cjtrowbridge/All-Seeing-Eye/3d models/design/cc1101/c2f52c2afb3fe4cf12543e919a84cf52887175e8_2_690x293.png

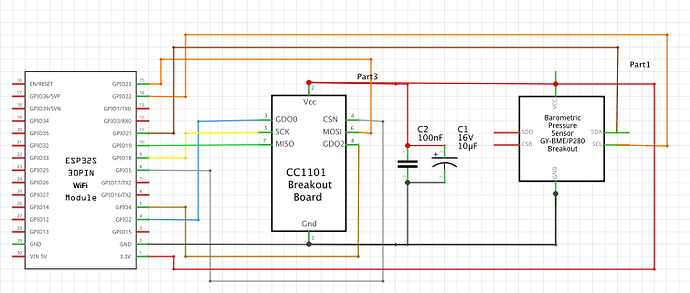
3d models/design/cc1101/c2f52c2afb3fe4cf12543e919a84cf52887175e8_2_690x293.png
