cjtrowbridge/All-Seeing-Eye/3d models/design/cc1101/images.jpg

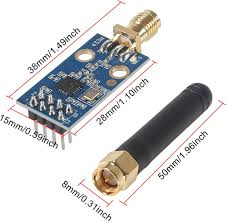
3d models/design/cc1101/images.jpg
