cjtrowbridge/All-Seeing-Eye/3d models/design/esp/616AZvK9qwL._AC_SL1200_.jpg

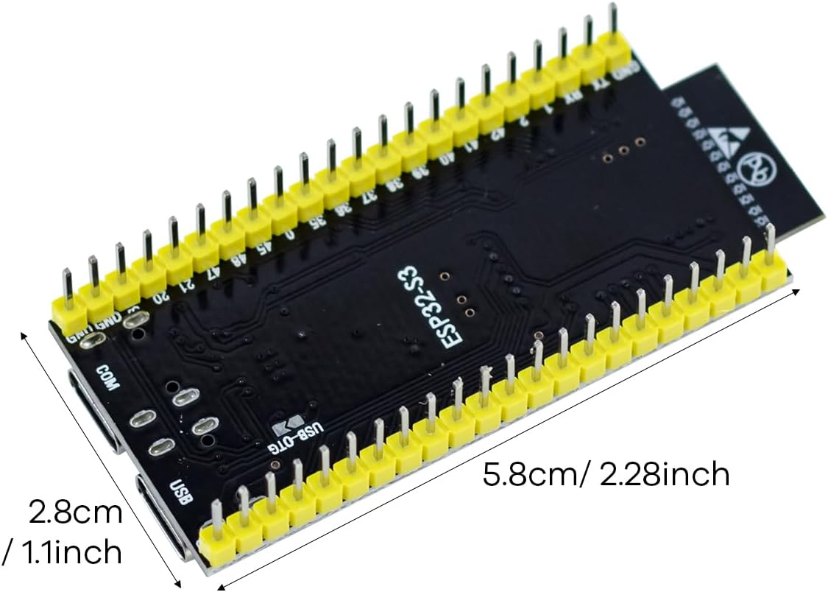
3d models/design/esp/616AZvK9qwL._AC_SL1200_.jpg
