cjtrowbridge/All-Seeing-Eye/3d models/design/esp/PXL_20260108_181501124.jpg

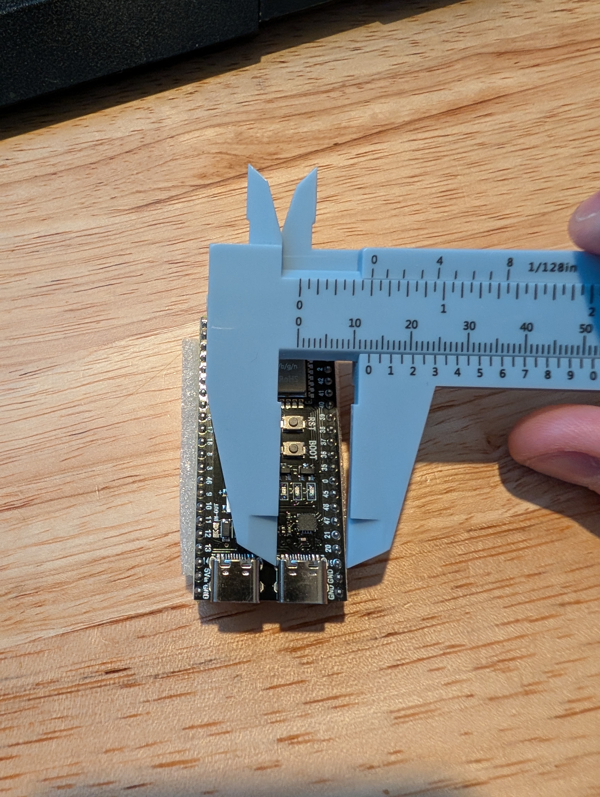
3d models/design/esp/PXL_20260108_181501124.jpg
