cjtrowbridge/All-Seeing-Eye/3d models/design/esp/PXL_20260108_181535649.jpg

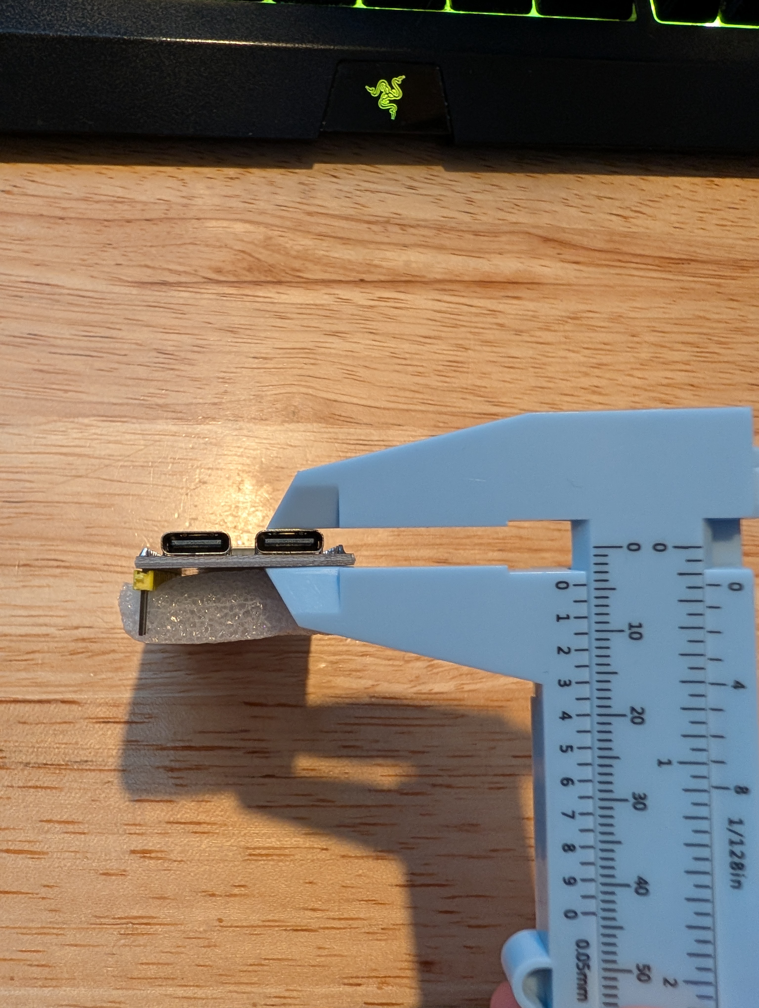
3d models/design/esp/PXL_20260108_181535649.jpg
