cjtrowbridge/All-Seeing-Eye/3d models/design/esp/PXL_20260110_050137347.jpg

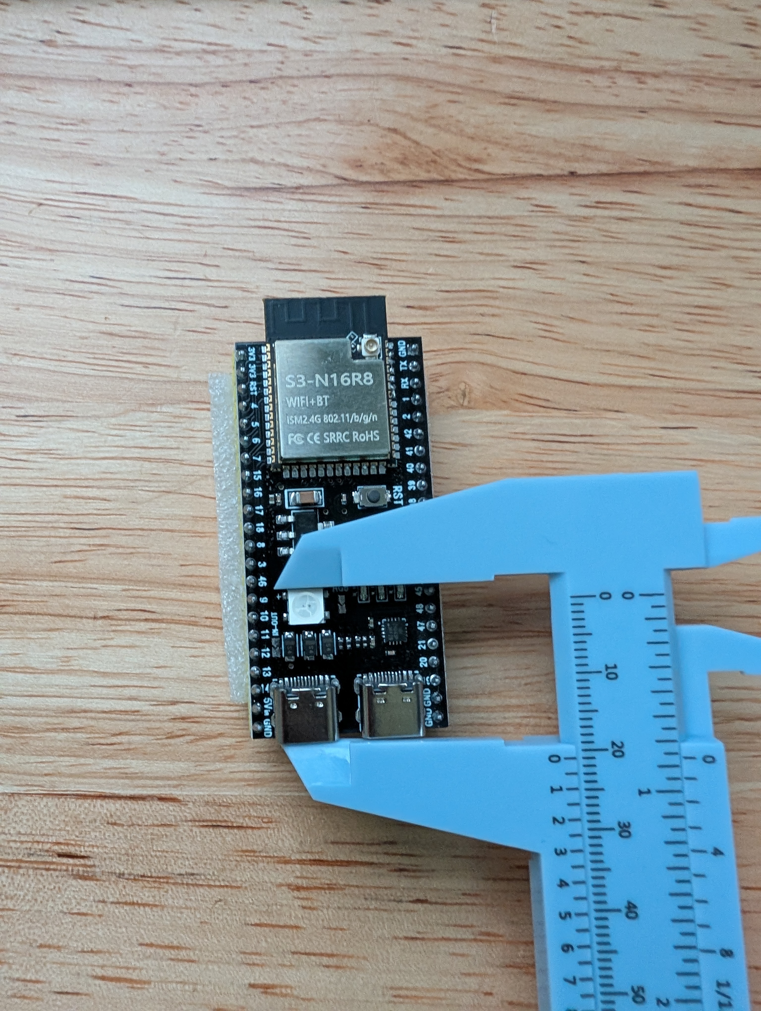
3d models/design/esp/PXL_20260110_050137347.jpg
