cjtrowbridge/All-Seeing-Eye/3d models/design/esp/PXL_20260110_050159167.jpg

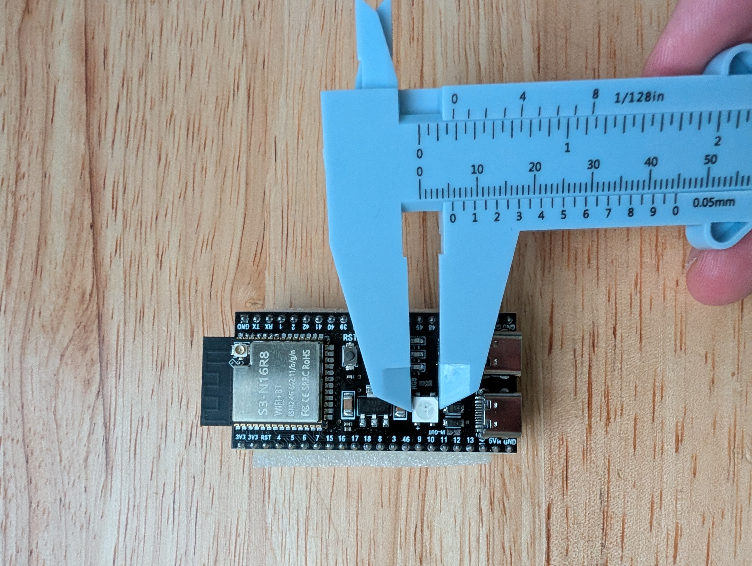
3d models/design/esp/PXL_20260110_050159167.jpg
