cjtrowbridge/All-Seeing-Eye/firmware/AllSeeingEye/src/WebStatic.h

#ifndef WEBSTATIC_H
#define WEBSTATIC_H

#include <Arduino.h>

const uint32_t index_html_gz_len = 15602;
const uint8_t index_html_gz[] PROGMEM = {
0x1F, 0x8B, 0x08, 0x00, 0xB3, 0xF0, 0x6A, 0x69, 0x02, 0xFF, 0xED, 0x7D, 0xED, 0x72, 0xE3, 0x46, 
0x92, 0xE0, 0xFF, 0x8D, 0xD8, 0x77, 0x28, 0xD3, 0x1E, 0x13, 0x6C, 0x93, 0x14, 0xA5, 0x6E, 0xF5, 
0xB6, 0xC9, 0x96, 0xBC, 0xB2, 0xA4, 0xB6, 0x75, 0xD3, 0x2D, 0xE9, 0x5A, 0xEA, 0xF1, 0x4E, 0x78, 
0x1D, 0xDB, 0x20, 0x59, 0xA4, 0xE0, 0x06, 0x01, 0x1A, 0x00, 0x25, 0xD1, 0xBD, 0xFC, 0x71, 0x4F, 
0x30, 0x71, 0x7F, 0x2F, 0x36, 0xE2, 0xE2, 0xFE, 0xDD, 0x23, 0xEC, 0xF3, 0xCC, 0x0B, 0xEC, 0x3D, 
0xC2, 0x65, 0x66, 0x15, 0x80, 0x02, 0x50, 0x55, 0x00, 0xD5, 0x1A, 0xCF, 0x4E, 0xC4, 0xB6, 0x6C, 
0x89, 0x04, 0xAA, 0xB2, 0xAA, 0xB2, 0xB2, 0xB2, 0xF2, 0xAB, 0xB2, 0x5E, 0x7E, 0x76, 0x72, 0x71, 
0x7C, 0xFD, 0xC7, 0xCB, 0x53, 0x76, 0x93, 0x2C, 0xFC, 0xC3, 0xBF, 0xFF, 0xBB, 0x97, 0xF8, 0x97, 
0xF9, 0x6E, 0x30, 0x3F, 0x68, 0xF1, 0xA0, 0x45, 0x4F, 0xB8, 0x3B, 0x85, 0xBF, 0x0C, 0xFE, 0xBD, 
0x5C, 0xF0, 0xC4, 0x65, 0x93, 0x1B, 0x37, 0x8A, 0x79, 0x72, 0xD0, 0x7A, 0x77, 0xFD, 0xAA, 0xF7, 
0xA2, 0x55, 0x78, 0x17, 0xB8, 0x0B, 0x7E, 0xD0, 0xBA, 0xF5, 0xF8, 0xDD, 0x32, 0x8C, 0x92, 0x16, 
0x9B, 0x84, 0x41, 0xC2, 0x03, 0x28, 0x7B, 0xE7, 0x4D, 0x93, 0x9B, 0x83, 0x29, 0xBF, 0xF5, 0x26, 
0xBC, 0x47, 0x5F, 0xBA, 0xCC, 0x0B, 0xBC, 0xC4, 0x73, 0xFD, 0x5E, 0x3C, 0x71, 0x7D, 0x7E, 0xB0, 
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
0xB9, 0xE3, 0x85, 0x11, 0xE1, 0x3F, 0xD7, 0xF7, 0xE6, 0x41, 0xCF, 0x03, 0x44, 0x03, 0x7E, 0x71, 
0x75, 0xF0, 0xA8, 0x54, 0x22, 0xA3, 0xC4, 0x24, 0x09, 0x17, 0x80, 0xB5, 0xE5, 0x3D, 0x8B, 0x43, 
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
};

#endif
