cjtrowbridge/All-Seeing-Eye/firmware/AllSeeingEye/src/WebServer.cpp

#include "WebServer.h"
#include <LittleFS.h>
#include "WebStatic.h" // Include generated HTML header
#include "BuildVersion.h" // Include generated Build ID
#include "Kernel.h" // For status access
#include "HAL.h" // Add HAL for Hardware Status
#include "Logger.h" // Add Logger
#include "RingBuffer.h" // Add RingBuffer
#include "PluginManager.h" // Add PluginManager
#include "PeerManager.h" // Add PeerManager
#include "Config.h" // Add Config
#include "AsyncJson.h" 
#include <ArduinoJson.h>
#include "Scheduler.h" // Add scheduler
#include "Geolocation.h"
#include "BleRangingManager.h"
#include <HTTPClient.h>

WebServerManager& WebServerManager::instance() {
    static WebServerManager _instance;
    return _instance;
}

WebServerManager::WebServerManager() : _server(80) {}

void WebServerManager::begin() {
    DefaultHeaders::Instance().addHeader("Access-Control-Allow-Origin", "*");
    
    setupRoutes();
    _server.begin();
    Serial.println("[Web] Async Server Started on Port 80");
}

void WebServerManager::setupRoutes() {
    // --------------------------------------------------
    // 1. Specific API Endpoints (Register First)
    // --------------------------------------------------

    // API: Status
    _server.on("/api/status", HTTP_GET, [this](AsyncWebServerRequest *request){
        static unsigned long lastStatusLog = 0;
        if (millis() - lastStatusLog > 10000) {
            Logger::instance().info("API", "GET /api/status");
            lastStatusLog = millis();
        }
        request->send(200, "application/json", this->getCachedStatus());
    });

    // API: Configuration (GET)
    _server.on("/api/config", HTTP_GET, [](AsyncWebServerRequest *request){
        Logger::instance().info("API", "GET /api/config");
        String response = Config::instance().getAllAsJson();
        request->send(200, "application/json", response);
    });

    // API: Configuration (POST)
    AsyncCallbackJsonWebHandler *handler = new AsyncCallbackJsonWebHandler("/api/config", [](AsyncWebServerRequest *request, JsonVariant &json) {
        Logger::instance().info("API", "POST /api/config");
        String jsonStr;
        serializeJson(json, jsonStr);
        
        if (Config::instance().updateFromJson(jsonStr)) {
            Logger::instance().info("Config", "Settings updated via API");
            JsonObject obj = json.as<JsonObject>();
            if (obj.containsKey("timezone")) {
                String timezone = Config::instance().getTimezone();
                Kernel::instance().applyTimezone(timezone);
                Logger::instance().info("Kernel", "Timezone updated: %s", timezone.c_str());
            }
            request->send(200, "application/json", "{\"status\":\"success\", \"message\":\"Config Updated. Reboot to apply network changes.\"}");
            // Optional: Config::instance().save(); // Preferences are auto-saved in close/put
        } else {
            Logger::instance().error("Config", "JSON parsing failed");
            request->send(400, "application/json", "{\"status\":\"error\", \"message\":\"Invalid JSON\"}");
        }
    });
    _server.addHandler(handler);

    // API: File System Index
    _server.on("/api/fs", HTTP_GET, [](AsyncWebServerRequest *request){
        Logger::instance().info("API", "GET /api/fs");
        JsonDocument doc;
        JsonArray files = doc.to<JsonArray>();

        File root = LittleFS.open("/");
        File file = root.openNextFile();
        while(file){
            JsonObject f = files.add<JsonObject>();
            f["name"] = String(file.name());
            f["size"] = file.size();
            file = root.openNextFile();
        }
        
        String response;
        serializeJson(doc, response);
        request->send(200, "application/json", response);
    });

    // API: Peers (Discovery)
    _server.on("/api/peers", HTTP_GET, [](AsyncWebServerRequest *request){
        Logger::instance().info("API", "GET /api/peers");
        // Passive Discovery: Check who is calling us
        PeerManager::instance().trackIncomingRequest(request->client()->remoteIP().toString());
        
        String response = PeerManager::instance().getPeersAsJson();
        request->send(200, "application/json", response);
    });

    // API: BLE Ranging (Latest Scan)
    _server.on("/api/ranging/ble", HTTP_GET, [](AsyncWebServerRequest *request){
        Logger::instance().info("API", "GET /api/ranging/ble");
        JsonDocument doc;
        JsonObject ble = doc.to<JsonObject>();
        BleRangingManager::instance().populateStatus(ble);
        String response;
        serializeJson(doc, response);
        request->send(200, "application/json", response);
    });

    // API: Utils - Ping
    _server.on("/api/ping", HTTP_GET, [](AsyncWebServerRequest *request){
        if (request->hasParam("target")) {
            String target = request->getParam("target")->value();
            Logger::instance().info("API", "GET /api/ping target=%s", target.c_str());
            bool result = PeerManager::instance().pingHost(target);
            
            JsonDocument doc;
            doc["target"] = target;
            doc["reachable"] = result;
            
            String res;
            serializeJson(doc, res);
            request->send(200, "application/json", res);
        } else {
            Logger::instance().warn("API", "GET /api/ping missing target");
            request->send(400, "application/json", "{\"error\":\"Missing 'target' parameter\"}");
        }
    });

    // API: System Head Logs (Startup Logs)
    // NOTE: Must be registered BEFORE /api/logs to avoid routing shadow
    _server.on("/api/logs/head", HTTP_GET, [](AsyncWebServerRequest *request){
        static unsigned long lastHeadLogsLog = 0;
        if (millis() - lastHeadLogsLog > 5000) {
            Logger::instance().info("API", "GET /api/logs/head");
            lastHeadLogsLog = millis();
        }
        JsonDocument doc;
        JsonArray logs = doc.to<JsonArray>();
        
        std::deque<String> logBuffer = Logger::instance().getHeadLogs();
        
        for(const auto& line : logBuffer) {
            logs.add(line);
        }
        
        String response;
        serializeJson(doc, response);
        request->send(200, "application/json", response);
    });

    // API: System Logs
    _server.on("/api/logs", HTTP_GET, [](AsyncWebServerRequest *request){
        static unsigned long lastLogsLog = 0;
        if (millis() - lastLogsLog > 5000) {
            Logger::instance().info("API", "GET /api/logs");
            lastLogsLog = millis();
        }
        JsonDocument doc;
        JsonArray logs = doc.to<JsonArray>();
        
        std::deque<String> logBuffer = Logger::instance().getLogs();
        
        // Return logs in insertion order
        for(const auto& line : logBuffer) {
            logs.add(line);
        }
        
        String response;
        serializeJson(doc, response);
        request->send(200, "application/json", response);
    });

    // --------------------------------------------------
    // API: Task Registry (Phase 5.1)
    // --------------------------------------------------

    // GET /api/task - Discovery
    _server.on("/api/task", HTTP_GET, [](AsyncWebServerRequest *request){
        Logger::instance().info("API", "GET /api/task");
        JsonDocument doc;
        JsonArray arr = doc.to<JsonArray>();
        
        std::vector<TaskDefinition> tasks = PluginManager::instance().getTaskCatalog();
        
        for(const auto& t : tasks) {
            JsonObject obj = arr.add<JsonObject>();
            obj["id"] = t.id;
            obj["name"] = t.name;
            obj["description"] = t.description;
            obj["plugin"] = t.pluginName;
            obj["link"] = t.endpoint;
            if (!t.inputs.empty()) {
                JsonArray inputs = obj.createNestedArray("inputs");
                for (const auto& input : t.inputs) {
                    JsonObject inputObj = inputs.add<JsonObject>();
                    inputObj["name"] = input.name;
                    inputObj["label"] = input.label;
                    inputObj["type"] = input.type;
                    if (input.required) {
                        inputObj["required"] = true;
                    }
                    if (input.defaultType == INPUT_VALUE_NUMBER) {
                        inputObj["default"] = input.defaultNumber;
                    } else if (input.defaultType == INPUT_VALUE_BOOL) {
                        inputObj["default"] = input.defaultBool;
                    } else if (input.defaultType == INPUT_VALUE_TEXT) {
                        inputObj["default"] = input.defaultText;
                    }
                    if (input.hasStep) {
                        inputObj["step"] = input.step;
                    }
                    if (input.hasMin) {
                        inputObj["min"] = input.min;
                    }
                    if (input.hasMax) {
                        inputObj["max"] = input.max;
                    }
                    if (!input.options.empty()) {
                        JsonArray options = inputObj.createNestedArray("options");
                        for (const auto& opt : input.options) {
                            JsonObject optObj = options.add<JsonObject>();
                            optObj["label"] = opt.label;
                            optObj["value"] = opt.value;
                        }
                    }
                }
            }
        }

        String response;
        serializeJson(doc, response);
        request->send(200, "application/json", response);
    });

    // POST /api/task/{taskId} - Execution
    // Note: We use a wildcard handler because AsyncWebServer doesn't do path params easily for *all* subpaths
    // But we defined specific endpoints in the catalog, so we can just match startsWith or use specific handlers.
    // For simplicity, we will register a generic handler for POST requests and parse the URL.
    
    // Instead of one generic handler which is messy, let's implement the specific routes from the catalog?
    // Cons: Duplication.
    // Pros: Explicit.
    
    // Better: One Handler for /api/task/* to give instructions
    _server.on("/api/task", HTTP_POST, [](AsyncWebServerRequest *request){
         request->send(400, "application/json", "{\"error\":\"Use specific task endpoints e.g. /api/task/ble-ranging/survey\"}");
    });
    
    // Loop to register handlers for catalog items
    std::vector<TaskDefinition> tasks = PluginManager::instance().getTaskCatalog();
    for(const auto& t : tasks) {
         AsyncCallbackJsonWebHandler *h = new AsyncCallbackJsonWebHandler(t.endpoint.c_str(), [t](AsyncWebServerRequest *request, JsonVariant &json) {
            Logger::instance().info("API", "Starting Task: %s", t.id.c_str());
            JsonObject params = json.as<JsonObject>();
            if (PluginManager::instance().startTask(t.id, params)) {
                 request->send(200, "application/json", "{\"status\":\"started\", \"taskId\":\"" + t.id + "\"}");
            } else {
                 request->send(500, "application/json", "{\"error\":\"Failed to start task\"}");
            }
        });
        _server.addHandler(h);
    }

    // --------------------------------------------------
    // API: Cluster Deploy / Start
    // --------------------------------------------------

    AsyncCallbackJsonWebHandler *deployHandler = new AsyncCallbackJsonWebHandler("/api/cluster/deploy", [](AsyncWebServerRequest *request, JsonVariant &json) {
        Logger::instance().info("API", "POST /api/cluster/deploy");
        JsonObject obj = json.as<JsonObject>();
        String taskId = obj["task"] | obj["id"] | "";

        JsonDocument paramsDoc;
        if (obj.containsKey("params")) {
            paramsDoc.set(obj["params"]);
        }

        if (taskId.length() == 0) {
            request->send(400, "application/json", "{\"error\":\"Missing task id\"}");
            return;
        }

        String paramsJson;
        serializeJson(paramsDoc, paramsJson);

        Kernel::instance().setDesiredTask(taskId, paramsJson);
        Kernel::instance().setStartRequested(false);

        JsonObject params = paramsDoc.as<JsonObject>();
        if (!PluginManager::instance().deployTask(taskId, params)) {
            request->send(500, "application/json", "{\"error\":\"Failed to deploy task\"}");
            return;
        }

        request->send(200, "application/json", "{\"status\":\"deploying\", \"taskId\":\"" + taskId + "\"}");
    });
    _server.addHandler(deployHandler);

    _server.on("/api/cluster/start", HTTP_POST, [](AsyncWebServerRequest *request) {
        Logger::instance().info("API", "POST /api/cluster/start");
        if (Kernel::instance().getDesiredTaskId().length() == 0) {
            request->send(400, "application/json", "{\"error\":\"No desired task staged\"}");
            return;
        }
        Kernel::instance().setStartRequested(true);
        PluginManager::instance().startStagedTask();
        request->send(200, "application/json", "{\"status\":\"started\"}");
    });

    _server.on("/api/report", HTTP_GET, [](AsyncWebServerRequest *request) {
        Logger::instance().info("API", "GET /api/report");
        bool localOnly = request->hasParam("local") && request->getParam("local")->value() == "1";
        static unsigned long lastReportLog = 0;
        const unsigned long now = millis();
        const bool logNow = (now - lastReportLog) > 5000;

        JsonDocument doc;
        JsonObject task = doc.createNestedObject("task");
        String desiredTaskId = Kernel::instance().getDesiredTaskId();
        String desiredParamsJson = Kernel::instance().getDesiredTaskParamsJson();
        if (desiredTaskId.length() > 0) {
            task["id"] = desiredTaskId;
            if (desiredParamsJson.length() > 0) {
                JsonDocument paramsDoc;
                DeserializationError err = deserializeJson(paramsDoc, desiredParamsJson);
                if (!err) {
                    task["params"] = paramsDoc.as<JsonObject>();
                }
            }
        }

        JsonObject nodes = doc.createNestedObject("nodes");

        // Self report
        String selfName = Config::instance().getHostname();
        JsonObject selfObj = nodes.createNestedObject(selfName);
        selfObj["task"] = PluginManager::instance().getActiveTaskName();
        ASEPlugin* active = PluginManager::instance().getActivePlugin();
        if (active) {
            JsonObject reportObj = selfObj.createNestedObject("report");
            if (!active->getJsonData(reportObj)) {
                selfObj.remove("report");
                if (logNow) {
                    Logger::instance().warn("Report", "No report data from plugin: %s", active->getName().c_str());
                }
            } else {
                if (logNow) {
                    Logger::instance().info("Report", "Report data collected from plugin: %s", active->getName().c_str());
                }
            }
        } else {
            if (logNow) {
                Logger::instance().warn("Report", "No active plugin for report");
            }
        }
        if (logNow) {
            lastReportLog = now;
        }

        if (!localOnly) {
            std::vector<Peer> peers;
            PeerManager::instance().getPeersSnapshot(peers);
            for (const auto& p : peers) {
                if (!p.online || p.ip.length() == 0) continue;

                HTTPClient http;
                http.setTimeout(1500);
                String url = "http://" + p.ip + "/api/report?local=1";
                http.begin(url);
                int code = http.GET();
                if (code == 200) {
                    String payload = http.getString();
                    JsonDocument peerDoc;
                    DeserializationError err = deserializeJson(peerDoc, payload);
                    if (!err) {
                        JsonObject peerNodes = peerDoc["nodes"];
                        if (!peerNodes.isNull()) {
                            for (JsonPair kv : peerNodes) {
                                nodes[kv.key().c_str()] = kv.value();
                            }
                        }
                    }
                }
                http.end();
            }
        }

        String response;
        serializeJson(doc, response);
        request->send(200, "application/json", response);
    });

    // --------------------------------------------------
    // API: LED Control
    // --------------------------------------------------
    
    // GET /api/led?r=255&g=0&b=0
    _server.on("/api/led", HTTP_GET, [](AsyncWebServerRequest *request){
        if(request->hasParam("r") && request->hasParam("g") && request->hasParam("b")) {
            int r = request->getParam("r")->value().toInt();
            int g = request->getParam("g")->value().toInt();
            int b = request->getParam("b")->value().toInt();
            Logger::instance().info("API", "GET /api/led r=%d g=%d b=%d", r, g, b);
            HAL::instance().setLed(r, g, b);
        } else {
            Logger::instance().warn("API", "GET /api/led missing rgb params");
        }
        
        // Return Status
        JsonDocument doc;
        doc["power"] = HAL::instance().getLedPower();
        JsonObject color = doc.createNestedObject("color");
        uint32_t c = HAL::instance().getLedColor();
        color["r"] = (c >> 16) & 0xFF;
        color["g"] = (c >> 8) & 0xFF;
        color["b"] = c & 0xFF;
        
        String res;
        serializeJson(doc, res);
        request->send(200, "application/json", res);
    });

    // POST /api/led/on
    _server.on("/api/led/on", HTTP_POST, [](AsyncWebServerRequest *request){
        Logger::instance().info("API", "POST /api/led/on");
        HAL::instance().setLedPower(true);
        request->send(200, "application/json", "{\"status\":\"success\", \"power\":true}");
    });

    // POST /api/led/off
    _server.on("/api/led/off", HTTP_POST, [](AsyncWebServerRequest *request){
        Logger::instance().info("API", "POST /api/led/off");
        HAL::instance().setLedPower(false);
        request->send(200, "application/json", "{\"status\":\"success\", \"power\":false}");
    });

    // --------------------------------------------------
    // API: Queue (Task Scheduler)
    // --------------------------------------------------
    _server.on("/api/queue", HTTP_GET, [](AsyncWebServerRequest *request){
        Logger::instance().info("API", "GET /api/queue");
        JsonDocument doc;
        
        // Current Task
        RadioTask current = Scheduler::instance().getCurrentTask();
        JsonObject currObj = doc.createNestedObject("current");
        currObj["id"] = current.id;
        currObj["name"] = current.taskName;
        currObj["plugin"] = current.pluginName;
        currObj["elapsed"] = millis() - current.startTime;
        currObj["duration"] = current.durationMs;
        
        // Queue
        JsonArray qArr = doc.createNestedArray("queue");
        std::deque<RadioTask> queue = Scheduler::instance().getQueue();
        for(const auto& t : queue) {
            JsonObject obj = qArr.add<JsonObject>();
            obj["id"] = t.id;
            obj["name"] = t.taskName;
            obj["plugin"] = t.pluginName;
            obj["type"] = (int)t.type;
        }

        String response;
        serializeJson(doc, response);
        request->send(200, "application/json", response);
    });

    // --------------------------------------------------
    // 2. Generic API Endpoint (Discovery)
    // --------------------------------------------------
    _server.on("/api", HTTP_GET, [](AsyncWebServerRequest *request){
        Logger::instance().info("API", "GET /api");
        JsonDocument doc;
        JsonArray routes = doc.to<JsonArray>();

        JsonObject r1 = routes.add<JsonObject>();
        r1["path"] = "/api";
        r1["method"] = "GET";
        r1["desc"] = "List available API endpoints";

        JsonObject r2 = routes.add<JsonObject>();
        r2["path"] = "/api/status";
        r2["method"] = "GET";
        r2["desc"] = "System health stats (RAM, Uptime)";

        JsonObject r3 = routes.add<JsonObject>();
        r3["path"] = "/api/config";
        r3["method"] = "GET/POST";
        r3["desc"] = "Get or Set system configuration";

        JsonObject r4 = routes.add<JsonObject>();
        r4["path"] = "/api/fs";
        r4["method"] = "GET";
        r4["desc"] = "List files in LittleFS";

        JsonObject r5 = routes.add<JsonObject>();
        r5["path"] = "/api/logs";
        r5["method"] = "GET";
        r5["desc"] = "Get system log buffer (Tail)";

        JsonObject r5a = routes.add<JsonObject>();
        r5a["path"] = "/api/logs/head";
        r5a["method"] = "GET";
        r5a["desc"] = "Get system startup logs (Head)";

        JsonObject r6 = routes.add<JsonObject>();
        r6["path"] = "/api/peers";
        r6["method"] = "GET";
        r6["desc"] = "Get discovered peers list";

        JsonObject rBle = routes.add<JsonObject>();
        rBle["path"] = "/api/ranging/ble";
        rBle["method"] = "GET";
        rBle["desc"] = "Get latest BLE ranging scan results";

        JsonObject rLed = routes.add<JsonObject>();
        rLed["path"] = "/api/led";
        rLed["method"] = "GET";
        rLed["desc"] = "Set LED usage: /api/led?r=255&g=0&b=0";

        JsonObject rPower = routes.add<JsonObject>();
        rPower["path"] = "/api/led/on";
        rPower["method"] = "POST";
        rPower["desc"] = "Enable LED output";

        JsonObject r7 = routes.add<JsonObject>();
        r7["path"] = "/api/queue";
        r7["method"] = "GET";
        r7["desc"] = "Inspect task scheduler state";

        JsonObject r8 = routes.add<JsonObject>();
        r8["path"] = "/api/reboot";
        r8["method"] = "POST";
        r8["desc"] = "Restart the device";

        String response;
        serializeJson(doc, response);
        request->send(200, "application/json", response);
    });

    // --------------------------------------------------
    // 3. Static Files (Embedded & FS Fallback)
    // --------------------------------------------------

    // Serve Embedded index.html (Compressed)
    auto rootHandler = [](AsyncWebServerRequest *request){
        AsyncWebServerResponse *response = request->beginResponse_P(200, "text/html", index_html_gz, index_html_gz_len);
        response->addHeader("Content-Encoding", "gzip");
        request->send(response);
    };
    
    _server.on("/", HTTP_GET, rootHandler);
    _server.on("/index.html", HTTP_GET, rootHandler);

    // Fallback: Serve other static files from LittleFS (if we add images later)
    _server.serveStatic("/assets", LittleFS, "/assets");

    // API: Reboot
    _server.on("/api/reboot", HTTP_POST, [](AsyncWebServerRequest *request){
        Logger::instance().info("API", "POST /api/reboot");
        request->send(200, "application/json", "{\"status\":\"success\", \"message\":\"Rebooting...\"}");
        // Delay slightly to let the response flush
        // We can't delay in async handler easily, but ESP.restart() is abrupt.
        // A timer or loop check in main might be better, but often this works enough to close socket.
        // For safety, we set a flag or just restart.
        
        // Quick & Dirty: Defer restart to main loop or just do it.
        // AsyncWebserver runs in a task. calling restart here *might* be okay but cleaner to defer.
        // Let's defer using a timer callback or just do it after short delay.
        
        xTaskCreate([](void*){ 
            vTaskDelay(pdMS_TO_TICKS(100)); // Allow response to send
            ESP.restart(); 
            vTaskDelete(NULL);
        }, "reboot", 2048, NULL, 5, NULL);
    });
}

String WebServerManager::getCachedStatus() {
    // Check Validity (Time based + existence)
    if (millis() - _lastCacheTime < _cacheDuration && _cachedStatus.length() > 0) {
        return _cachedStatus;
    }

    // Dynamic Allocation
    JsonDocument doc; 
    
    doc["uptime"] = millis();
    doc["heap_free"] = ESP.getFreeHeap();
    doc["heap_size"] = ESP.getHeapSize();
    doc["psram_free"] = ESP.getFreePsram();
    doc["psram_size"] = ESP.getPsramSize();
    doc["flash_size"] = ESP.getFlashChipSize();

    doc["hostname"] = Config::instance().getHostname();
    doc["description"] = Config::instance().getString("description", "");
    doc["build_id"] = BUILD_ID;
    doc["timezone"] = Kernel::instance().getTimezone();
    doc["time"] = (long long)Kernel::instance().getEpochTime();
    doc["ntp_sync"] = Kernel::instance().isTimeSynced();

    JsonObject geo = doc.createNestedObject("geolocation");
    GeolocationService::instance().populateStatus(geo);

    JsonObject bleRanging = doc.createNestedObject("ble_ranging");
    BleRangingManager::instance().populateStatus(bleRanging);
    
    doc["rb_capacity"] = RingBuffer::instance().capacity();
    doc["rb_usage"] = RingBuffer::instance().available();

    doc["plugin"] = PluginManager::instance().getActivePluginName();

    // Desired Task Coordination
    String desiredTaskId = Kernel::instance().getDesiredTaskId();
    String desiredParamsJson = Kernel::instance().getDesiredTaskParamsJson();
    if (desiredTaskId.length() > 0) {
        JsonObject desired = doc.createNestedObject("desired_task");
        desired["id"] = desiredTaskId;
        if (desiredParamsJson.length() > 0) {
            JsonDocument paramsDoc;
            DeserializationError err = deserializeJson(paramsDoc, desiredParamsJson);
            if (!err) {
                desired["params"] = paramsDoc.as<JsonObject>();
            }
        }
    }
    doc["start_requested"] = Kernel::instance().isStartRequested();

    // Hardware Status
    JsonObject hw = doc.createNestedObject("hardware");
    hw["cc1101"] = HAL::instance().hasRadio();
    hw["gps"] = HAL::instance().hasGPS();
    hw["meshtastic"] = HAL::instance().hasMeshtastic();

    // LED Status
    JsonObject led = doc.createNestedObject("led");
    led["power"] = HAL::instance().getLedPower();
    JsonObject color = led.createNestedObject("color");
    uint32_t c = HAL::instance().getLedColor();
    color["r"] = (c >> 16) & 0xFF;
    color["g"] = (c >> 8) & 0xFF;
    color["b"] = c & 0xFF;

    // Calculate System Status
    String statusMsg = "Ready";
    if (!HAL::instance().hasRadio()) {
        statusMsg = "Radio Problem: Failed To POST";
    } else {
        if (desiredTaskId.length() > 0 && !Kernel::instance().isStartRequested()) {
            statusMsg = "Ready";
        } else {
            String pName = PluginManager::instance().getActivePluginName();
            if (pName == "SystemIdle") {
                statusMsg = "Ready";
            } else if (pName == "RadioTest") {
                statusMsg = "Working: Hardware Verification";
            } else if (PluginManager::instance().isTaskRunning()) {
                statusMsg = "Working: " + pName;
            } else {
                statusMsg = "Ready";
            }
        }
    }
    doc["status"] = statusMsg;
    doc["task"] = PluginManager::instance().getActiveTaskName();
    doc["clusterName"] = Config::instance().getString("cluster", "Default");

    // Queue Status
    RadioTask current = Scheduler::instance().getCurrentTask();
    JsonObject queueObj = doc.createNestedObject("queue");
    JsonObject qCurr = queueObj.createNestedObject("current");
    qCurr["id"] = current.id;
    qCurr["plugin"] = current.pluginName;
    qCurr["task"] = current.taskName;
    qCurr["elapsed"] = millis() - current.startTime;
    qCurr["duration"] = current.durationMs;
    queueObj["depth"] = Scheduler::instance().getQueue().size();

    // Aggregated Data
    JsonArray peers = doc.createNestedArray("peers");
    PeerManager::instance().populatePeers(peers);

    JsonArray logs = doc.createNestedArray("logs");
    Logger::instance().populateLogs(logs);

    String response;
    serializeJson(doc, response);
    
    // Update Cache
    _cachedStatus = response;
    _lastCacheTime = millis();
    
    return response;
}
