cjtrowbridge/All-Seeing-Eye/firmware/AllSeeingEye/src/WebServer.h

#ifndef WEBSERVER_AS_H
#define WEBSERVER_AS_H

#include <Arduino.h>
#include <ESPAsyncWebServer.h>
#include <ArduinoJson.h>

class WebServerManager {
public:
    static WebServerManager& instance();
    void begin();
    
private:
    WebServerManager();
    AsyncWebServer _server;
    
    void setupRoutes();
    
    // Cache System
    String _cachedStatus;
    unsigned long _lastCacheTime = 0;
    const unsigned long _cacheDuration = 500; // Cache for 500ms
    String getCachedStatus();
};

#endif
