cjtrowbridge/All-Seeing-Eye/firmware/AllSeeingEye/secrets.example.h

#ifndef WIFI_SECRETS_H
#define WIFI_SECRETS_H

// WiFi Configuration
// Rename this file to wifi.h and update with your credentials

const char* ssid = "YOUR_SSID_HERE";
const char* password = "YOUR_PASSWORD_HERE";

#endif
